SRA-VJTI/TitanLegs/Mechanical_Design/Leg_Design/2_Upper_Limb_Connector.STL

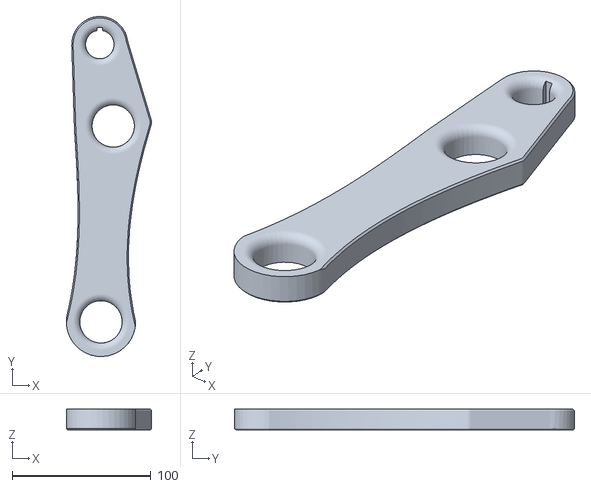
[picture p21: CAD file, 2021-11-09]
Mechanical_Design/Leg_Design/2_Upper_Limb_Connector.STL
61.5 x 245.2 x 15.0
