SRA-VJTI/TitanLegs/Mechanical_Design/Gearbox_STL/Out_Box.STL

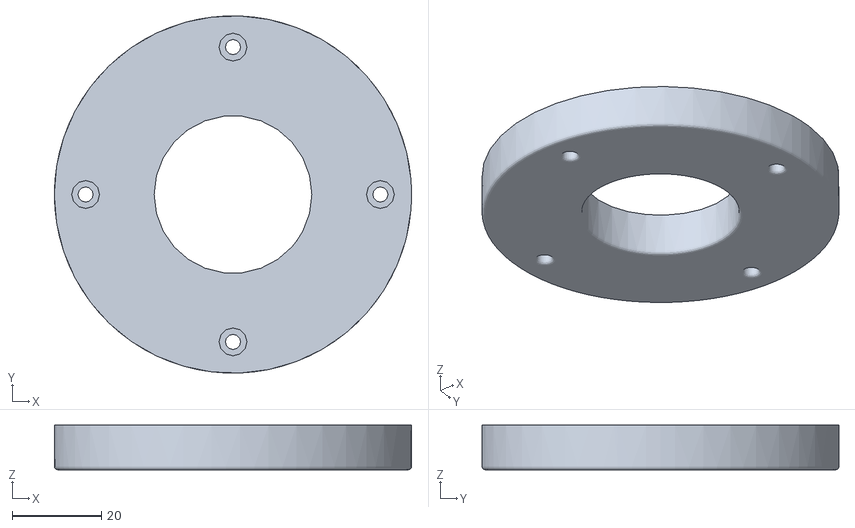
[picture p22: CAD file, 2023-01-26]
Mechanical_Design/Gearbox_STL/Out_Box.STL
80.0 x 79.9 x 10.0
