SRA-VJTI/TitanLegs/Mechanical_Design/Leg_Design/6_Wire_Clamp_Bottom.STL

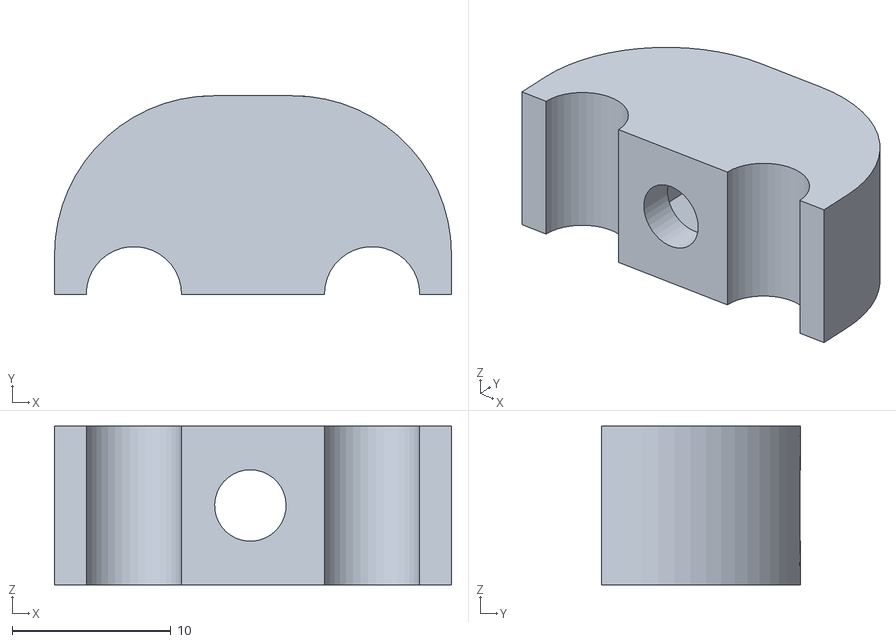
[picture p23: CAD file, 2021-11-09]
Mechanical_Design/Leg_Design/6_Wire_Clamp_Bottom.STL
25.0 x 12.5 x 10.0
