SRA-VJTI/TitanLegs/Mechanical_Design/Gearbox_STL/Combined_Box.STL

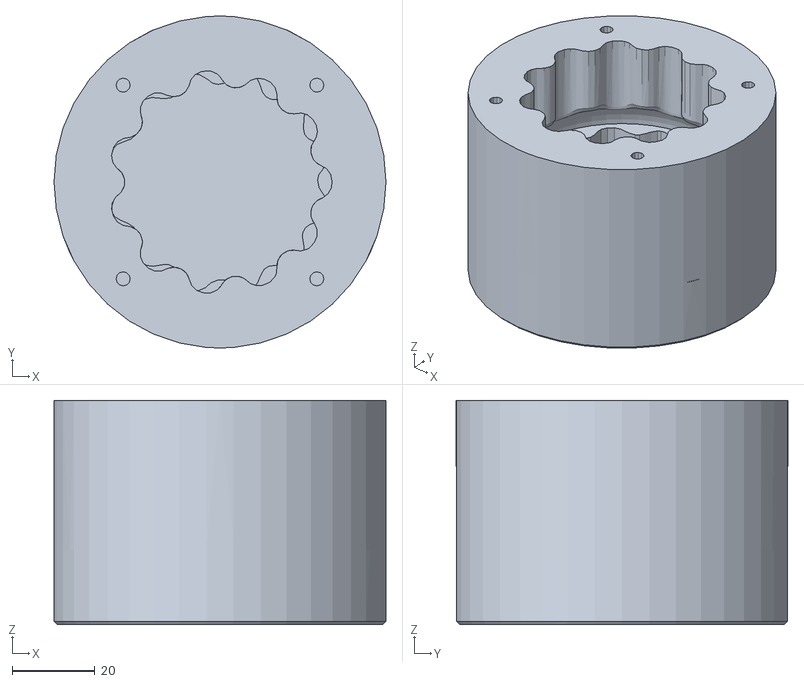
[picture p24: CAD file, 2023-01-26]
Mechanical_Design/Gearbox_STL/Combined_Box.STL
80.0 x 80.0 x 54.0
