SRA-VJTI/TitanLegs/Mechanical_Design/Gearbox_STL/Rotor_10.STL

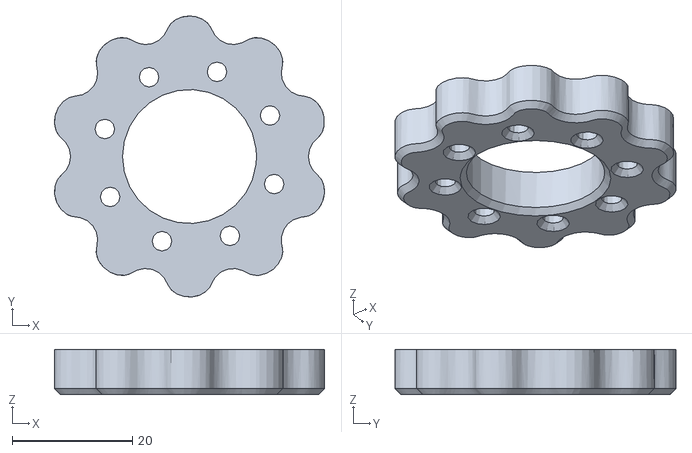
[picture p25: CAD file, 2023-01-26]
Mechanical_Design/Gearbox_STL/Rotor_10.STL
44.8 x 46.7 x 7.50
