SRA-VJTI/TitanLegs/Mechanical_Design/Gearbox_STL/New_shaft_2.STL

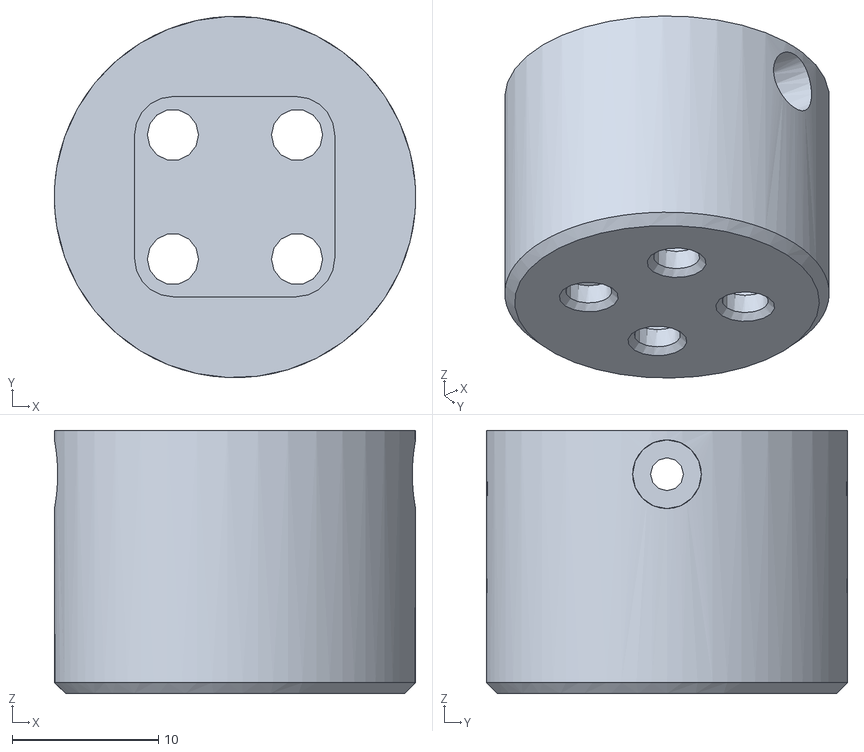
[picture p26: CAD file, 2023-01-26]
Mechanical_Design/Gearbox_STL/New_shaft_2.STL
24.7 x 24.7 x 18.0
