SRA-VJTI/TitanLegs/Mechanical_Design/Gearbox_STL/New_Shaft_1.STL

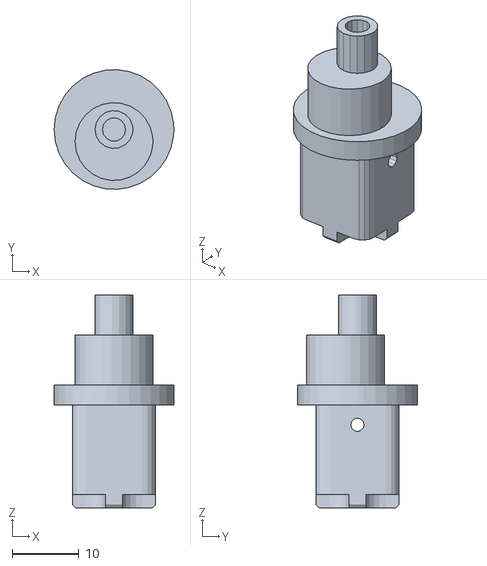
[picture p27: CAD file, 2023-01-26]
Mechanical_Design/Gearbox_STL/New_Shaft_1.STL
18.0 x 18.0 x 32.0
