SRA-VJTI/TitanLegs/Mechanical_Design/Gearbox_STL/Output_Disk.STL

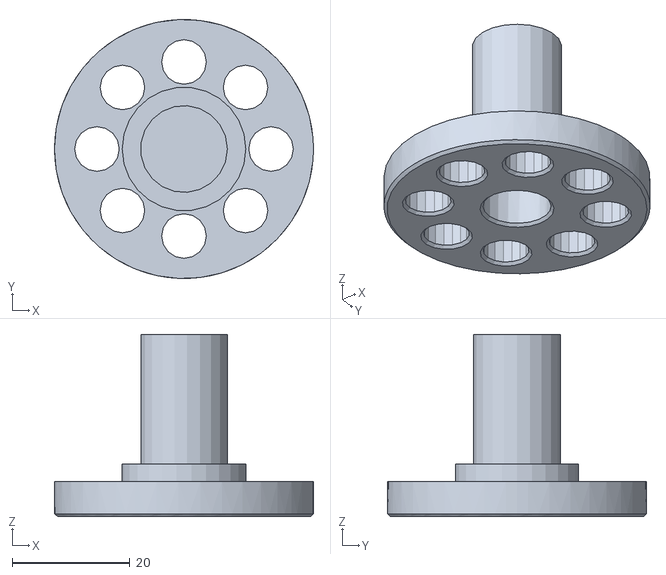
[picture p28: CAD file, 2023-01-26]
Mechanical_Design/Gearbox_STL/Output_Disk.STL
44.0 x 44.0 x 31.0
